adaand00/christmas-banana-synth/Code/stylophone-xmas/src/songs.h

#include <Arduino.h>

// Song data as 2D array of [note, duration]
// Note: 1 is a C4, 24 is a B6, etc. 0 is a rest (no sound) 
// Duration: note/rest time in milliseconds

typedef struct {
  uint8_t note;
  uint16_t duration;
} note_t;

// Last christmas:
const note_t last_christmas[] = {{17,737},{0,64},{17,438},{0,93},{15,108},{0,427},{10,60},{0,206},{17,193},{0,73},{17,202},{0,65},{19,161},{0,107},{15,578},{0,222},{12,191},{0,75},{12,165},{0,97},{17,214},{0,51},{17,198},{0,70},{19,180},{0,354},{15,571},{0,225},{12,64},{0,204},{14,247},{0,20},{15,266},{0,0},{14,208},{0,60},{12,880},{0,455},{19,681},{0,120},{17,806},{0,261},{12,77},{0,191},{19,197},{0,66},{20,194},{0,72},{19,166},{0,101},{17,697},{0,376},{15,63},{0,202},{14,246},{0,21},{15,207},{0,58},{14,63},{0,207},{14,412},{0,120},{15,90},{0,446},{14,218},{0,318},{10,936}};
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
const note_t march[] = {{5, 281}, {0, 206}, {5, 307}, {0, 197}, {5, 312}, {0, 171}, {1, 244}, {0, 125}, {8, 67}, {0, 60}, {5, 416}, {0, 165}, {1, 287}, {0, 169}, {8, 85}, {0, 51}, {5, 747}, {0, 422}, {12, 377}, {0, 216}, {12, 371}, {0, 208}, {12, 386}, {0, 223}, {13, 257}, {0, 165}, {8, 95}, {0, 69}, {4, 416}, {0, 156}, {1, 248}, {0, 176}, {8, 85}, {0, 79}, {5, 514}, {0, 655}, {17, 457}, {0, 131}, {5, 297}, {0, 161}, {5, 116}, {0, 34}, {17, 371}, {0, 164}, {16, 318}, {0, 153}, {15, 98}, {0, 49}, {14, 140}, {0, 6}, {13, 101}, {0, 45}, {14, 132}, {0, 468}, {6, 113}, {0, 183}, {11, 389}, {0, 198}, {10, 322}, {0, 118}, {9, 83}, {0, 57}, {8, 113}, {0, 26}, {7, 89}, {0, 60}, {8, 128}, {0, 475}, {1, 98}, {0, 192}, {4, 355}, {0, 230}, {1, 337}, {0, 116}, {8, 73}, {0, 61}, {5, 398}, {0, 177}, {1, 330}, {0, 140}, {8, 79}, {0, 49}, {5, 741}};

const note_t * songs[] = {
  last_christmas,
  jingle,
  i_want, 
  rockin,
  feliz,
  wish_merry,
  silent,
  funky,
  groove,
  rickroll, 
  mario, 
  march
};

size_t sn = sizeof(note_t);

const uint32_t song_lengths[] = {
  sizeof(last_christmas)/sn,
  sizeof(jingle)/sn,
  sizeof(i_want)/sn,
  sizeof(rockin)/sn,
  sizeof(feliz)/sn,
  sizeof(wish_merry)/sn,
  sizeof(silent)/sn,
  sizeof(funky)/sn,
  sizeof(groove)/sn,
  sizeof(rickroll)/sn,
  sizeof(mario)/sn,
  sizeof(march)/sn
};
